burro-jockey/kennyvision/assets_for_svgs/design-0b58fb78-c69b-4962-ab3e-5e4547d4a51a - Copy.png

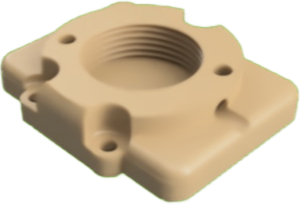
assets_for_svgs/design-0b58fb78-c69b-4962-ab3e-5e4547d4a51a - Copy.png
