burro-jockey/kennyvision/assets_for_svgs/design-626016c2-ed3d-46e3-a777-ed3c7ec89ee0.png

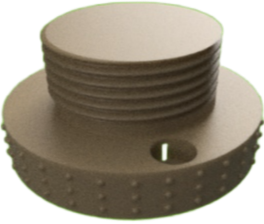
assets_for_svgs/design-626016c2-ed3d-46e3-a777-ed3c7ec89ee0.png
