burro-jockey/kennyvision/assets_for_svgs/design-24546543-da1a-46a1-ae5a-5792af293df7 - Copy.png

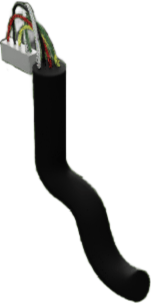
assets_for_svgs/design-24546543-da1a-46a1-ae5a-5792af293df7 - Copy.png
