burro-jockey/kennyvision/assets_for_svgs/design-b6035e9a-b9b0-422b-8c73-df4a288b01c6 - Copy.png

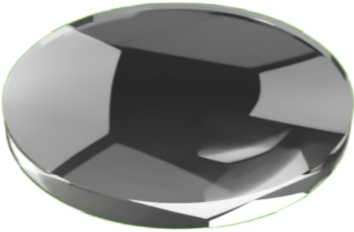
assets_for_svgs/design-b6035e9a-b9b0-422b-8c73-df4a288b01c6 - Copy.png
