burro-jockey/kennyvision/assets_for_svgs/design-d6e184ca-b631-49e7-b73f-e5f6adb39619.png

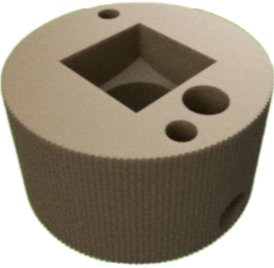
assets_for_svgs/design-d6e184ca-b631-49e7-b73f-e5f6adb39619.png
