burro-jockey/kennyvision/assets_for_svgs/design-d21aceb9-7397-43f9-8c97-36090870cc97.png

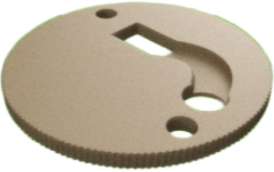
assets_for_svgs/design-d21aceb9-7397-43f9-8c97-36090870cc97.png
