burro-jockey/kennyvision/assets_for_svgs/design-f1e317fd-9368-461d-97bb-055488b7019b.png

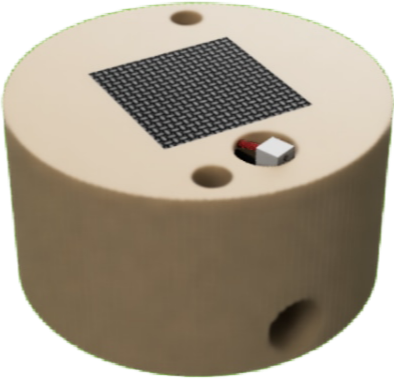
assets_for_svgs/design-f1e317fd-9368-461d-97bb-055488b7019b.png
