burro-jockey/kennyvision/assets_for_svgs/image-removebg-preview (1) - Copy.png

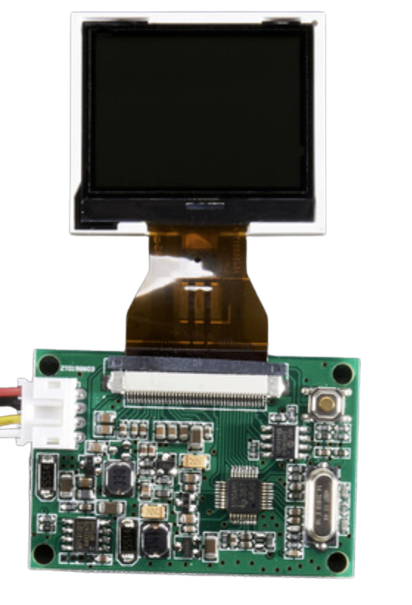
assets_for_svgs/image-removebg-preview (1) - Copy.png
