burro-jockey/kennyvision/assets_for_svgs/image-removebg-preview (2) - Copy.png

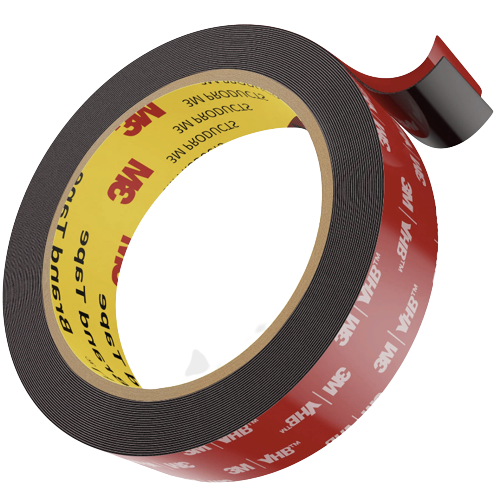
assets_for_svgs/image-removebg-preview (2) - Copy.png
