burro-jockey/kennyvision/assets_for_svgs/image-removebg-preview - Copy.png

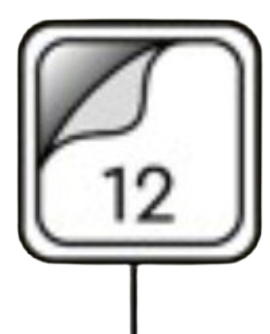
assets_for_svgs/image-removebg-preview - Copy.png
