burro-jockey/kennyvision/assets_for_svgs/kennyvision_2023-Apr-12_04-06-26AM-000_CustomizedView1086146623-removebg-preview - Copy.png

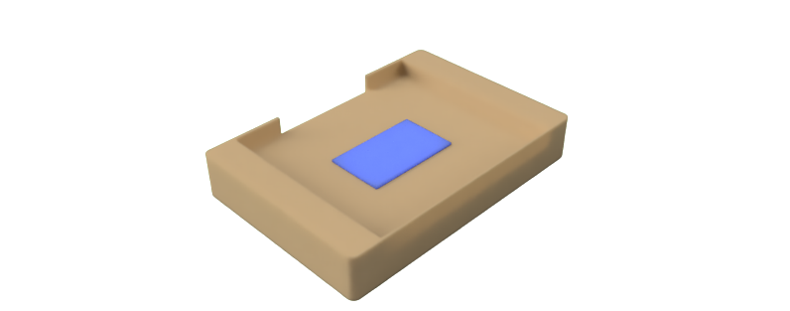
assets_for_svgs/kennyvision_2023-Apr-12_04-06-26AM-000_CustomizedView1086146623-removebg-preview - Copy.png
