burro-jockey/kennyvision/assets_for_svgs/kennyvision_2023-Apr-12_04-23-25AM-000_CustomizedView44683921407-removebg-preview - Copy.png

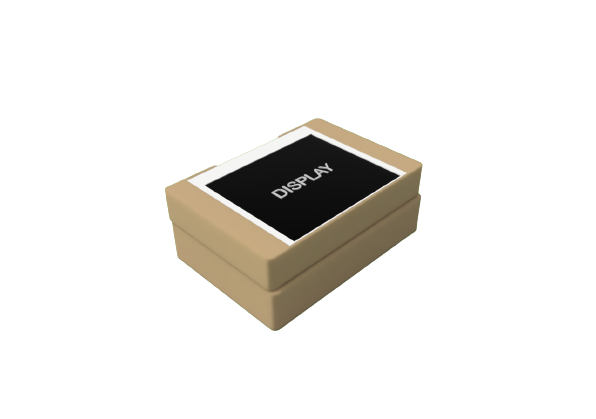
assets_for_svgs/kennyvision_2023-Apr-12_04-23-25AM-000_CustomizedView44683921407-removebg-preview - Copy.png
