burro-jockey/kennyvision/assets_for_svgs/kennyvision_2023-Apr-12_04-39-51AM-000_CustomizedView59896285-removebg-preview - Copy.png

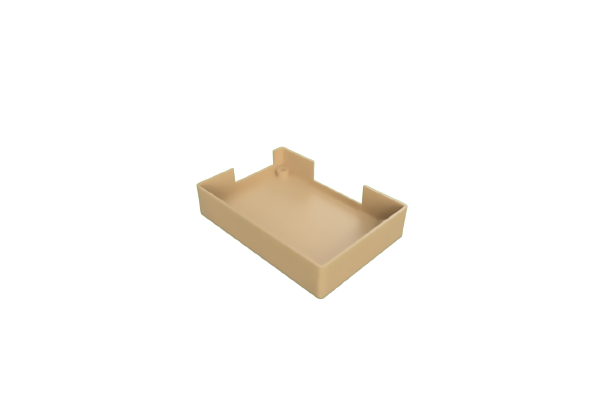
assets_for_svgs/kennyvision_2023-Apr-12_04-39-51AM-000_CustomizedView59896285-removebg-preview - Copy.png
