burro-jockey/kennyvision/assets_for_svgs/kennyvision_v7-removebg-preview - Copy.png

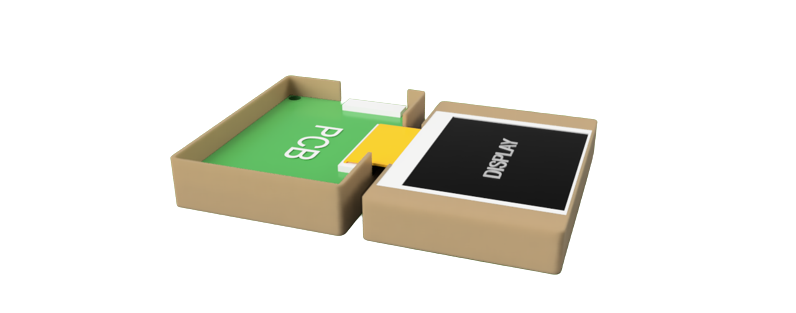
assets_for_svgs/kennyvision_v7-removebg-preview - Copy.png
