burro-jockey/kennyvision/assets_for_svgs/render_a-removebg-preview (1) - Copy.png

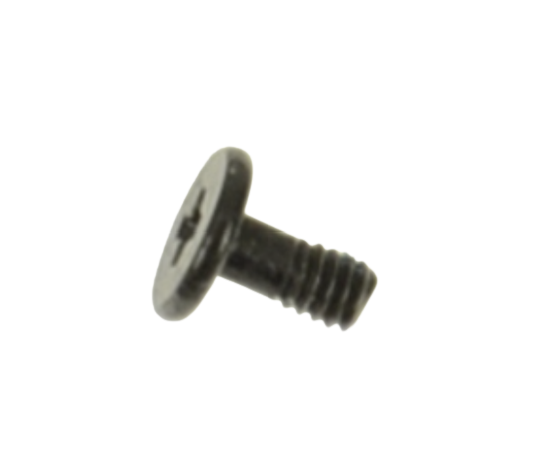
assets_for_svgs/render_a-removebg-preview (1) - Copy.png
