burro-jockey/kennyvision/assets_for_svgs/render_a-removebg-preview.png

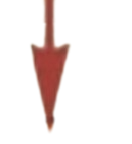
assets_for_svgs/render_a-removebg-preview.png
