burro-jockey/kennyvision/Page 7.png

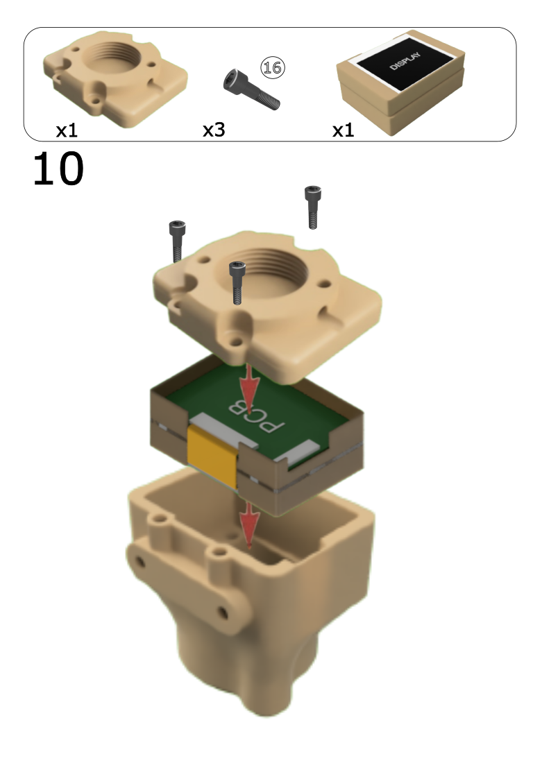
Page 7.png
